davidlibland/soldano-brown/ACTRIMS Model Image.skt/Layer~1.png

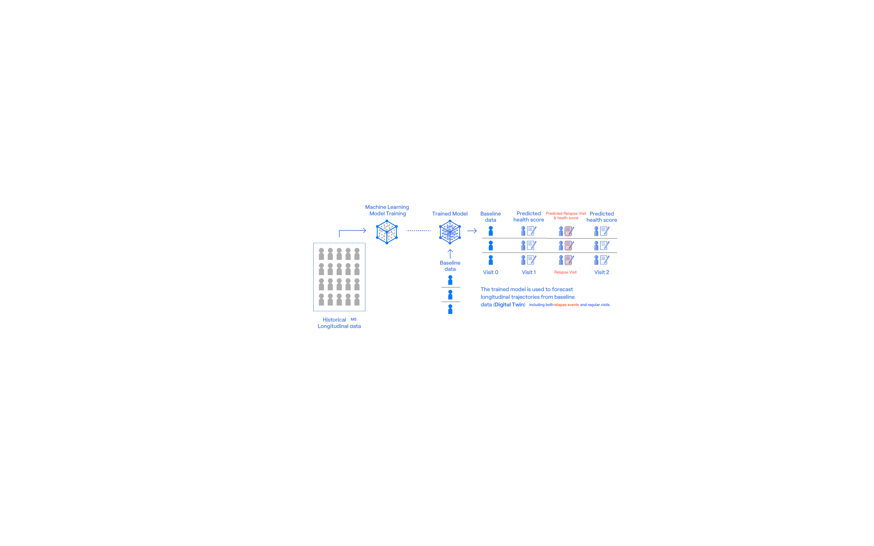
ACTRIMS Model Image.skt/Layer~1.png
