davidlibland/soldano-brown/single tube.png

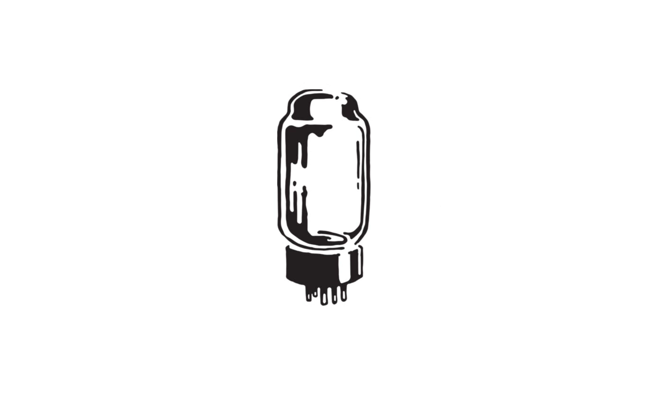
single tube.png
