davidlibland/soldano-brown/SLOstortion Circuit.jpeg

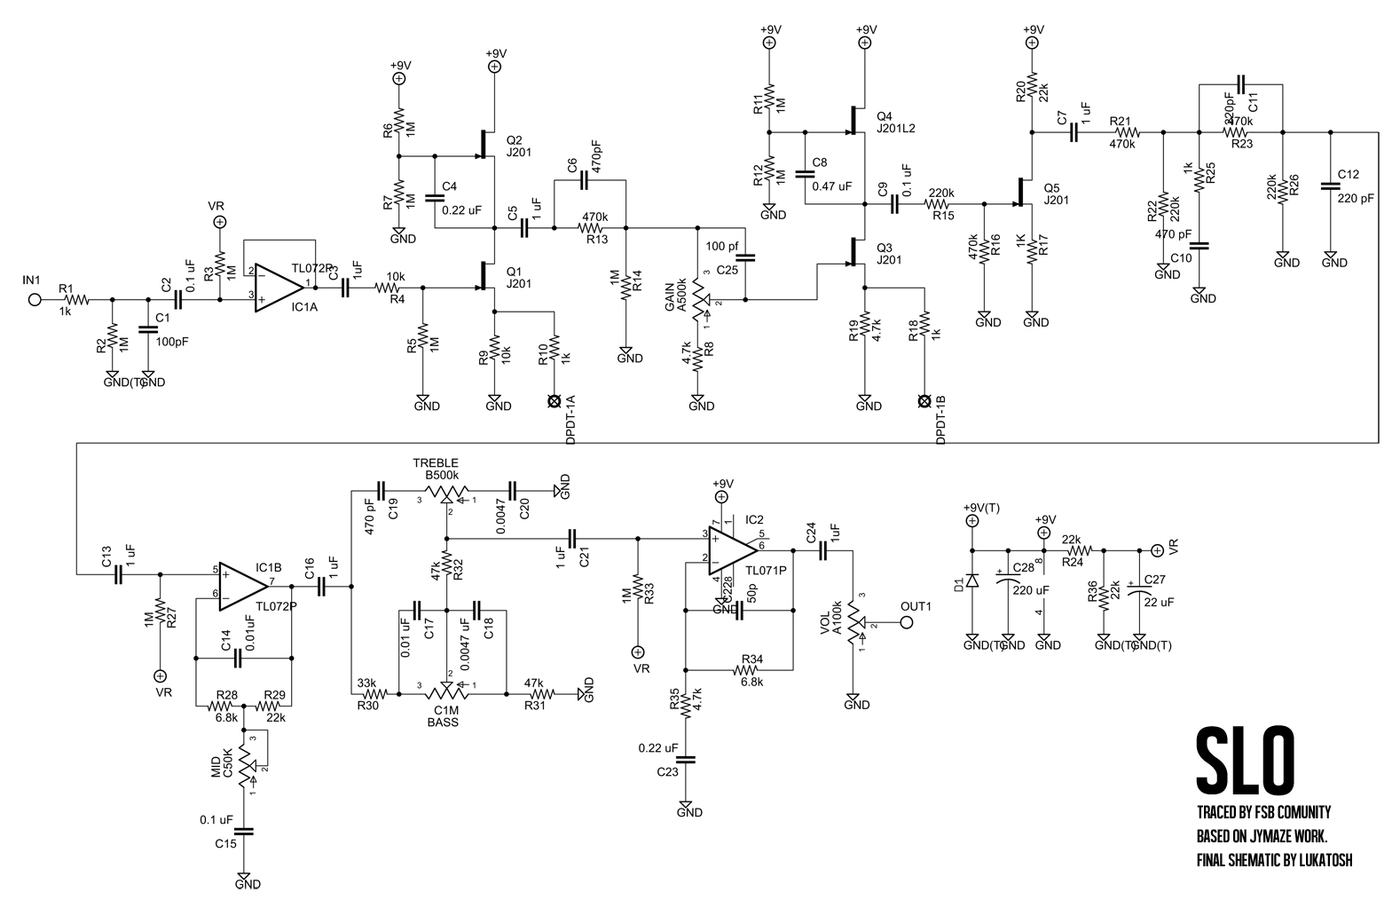
SLOstortion Circuit.jpeg
