davidlibland/soldano-brown/slostortion schema.png

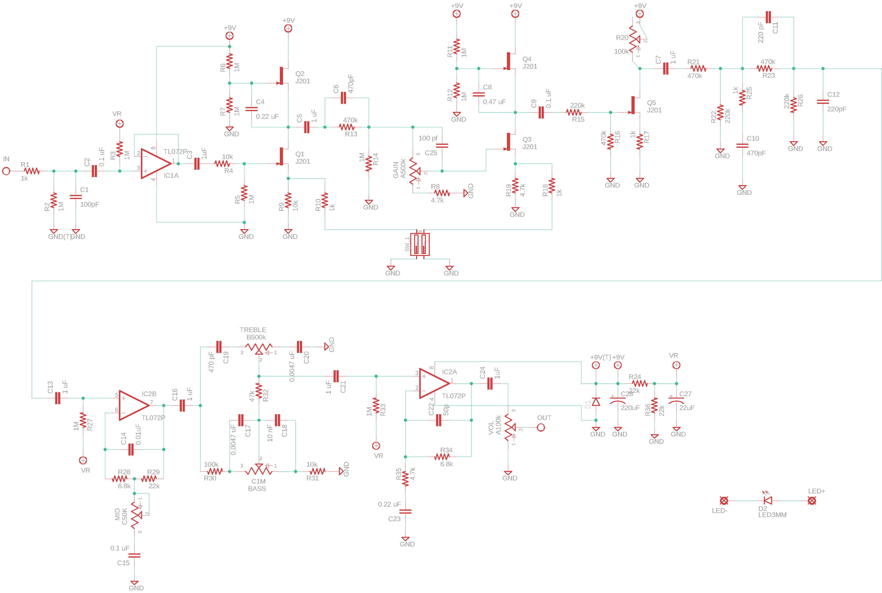
slostortion schema.png
