davidlibland/soldano-brown/slostortion_v1.png

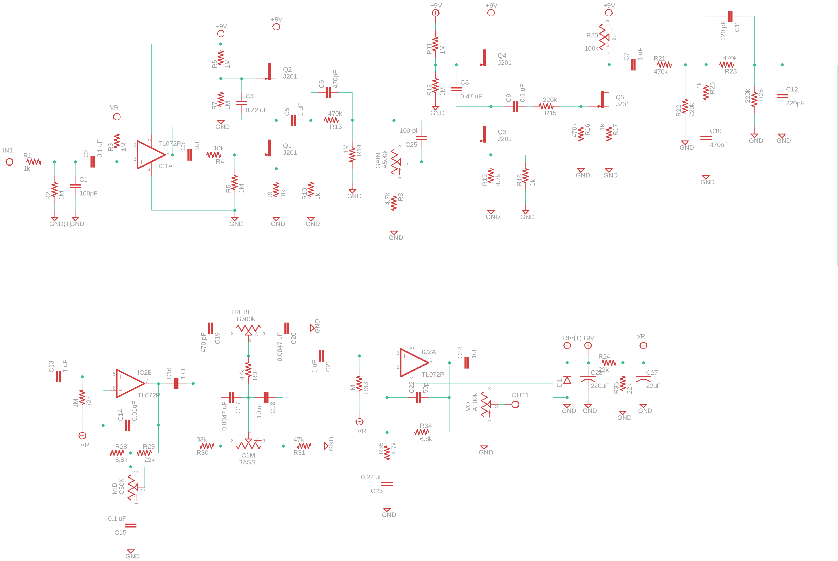
slostortion_v1.png
