davidlibland/soldano-brown/Wampler SLOstortion.png

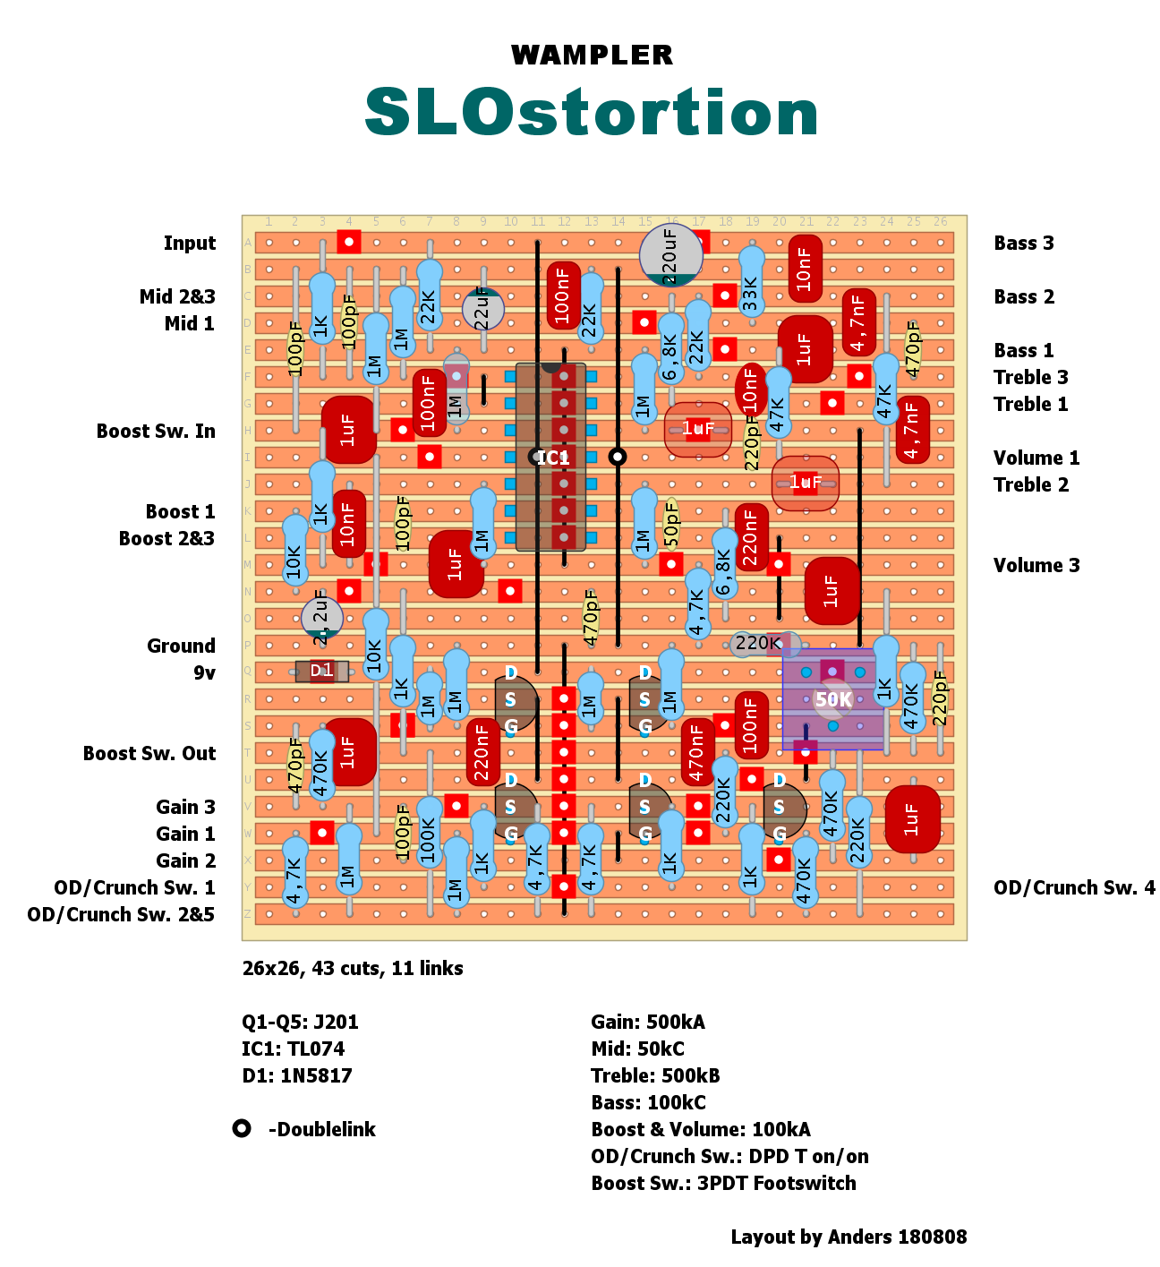
Wampler SLOstortion.png
